xiahualiu/biron/KiCAD/pdf/biron-sch.pdf

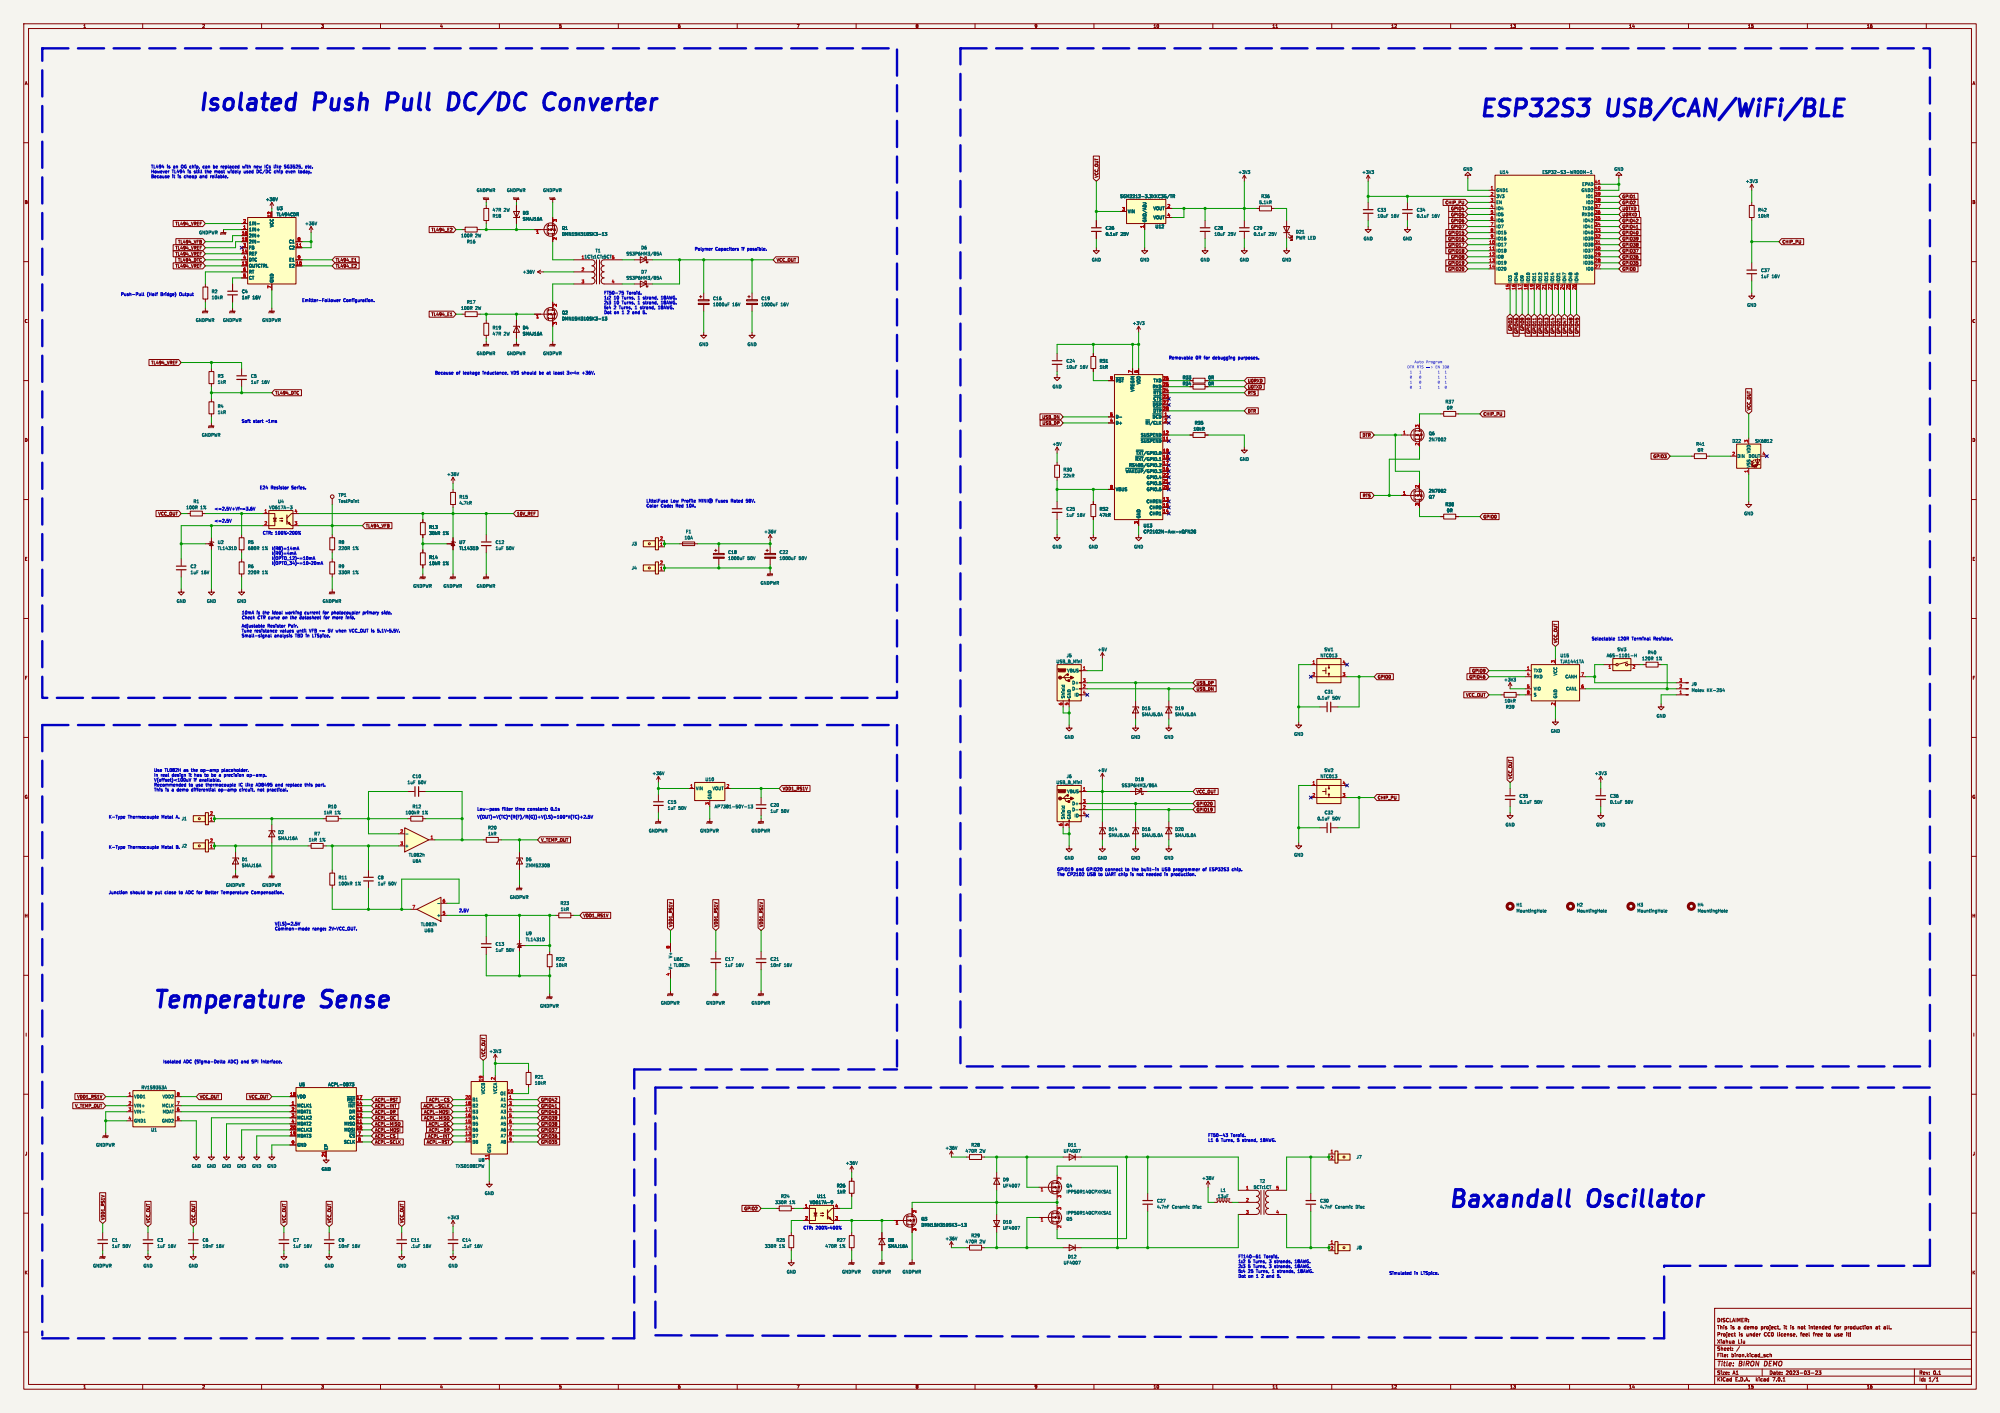
[picture p15: page 1]

Soft start ~1ms Isolated Push Pull DC/DC Converter

V(OUT)=V(TC)*(R(F)/R(G))+V(LS)=100*V(TC)+2.5V

ACPL-RST
ACPL-INT ACPL-DR
GPIO40 ACPL-OC

ACPL-INT ACPL-MOSI ACPL-RST
ACPL-MISO
ACPL-OC

ACPL-MOSI ACPL-SCLK

Id: 1/1 Title: BIRON DEMO
