xiahualiu/biron/LTSpice/Baxandall.asc

C1: cap; 1n; V=630 Irms=0 Rser=1m Lser=0
C2: cap; 4.7n; V=630 Irms=0 Rser=1m Lser=0
D1: diode; uf4007
D2: diode; uf4007
D3: zener; TFZV16B
D4: zener; TFZV16B
L1: ind2; 5µ; Rser=0.001
L2: ind2; 5µ; Rser=0.001
L3: ind2; 125µ; Rser=0.005
L4: ind; 24µ; Ipk=20 Rser=0.01 Rpar=0 Cpar=0
L5: ind; 10µ; Ipk=32 Rser=0.00567 Rpar=13284 Cpar=14.992p
M1: nmos; IPP50R190CE_L0
M3: nmos; IPP50R190CE_L0
R6: res; 470
R7: res; 470
V1: voltage; 36; Rser=0
Named nets: 0
.include components/UF4007.lib
.tran 1m startup
K1 L1 L2 L3 0.99
.include components/IPP50R380CE.lib
